MANUEL-Enzo/GameDuino/Organisation Projet/Cahier Des Charges Gameduino.docx

BENHARRATS Amine G4

MANUEL Enzo 2019/2020

CAHIER DES CHARGES :

Présentation :

Gameduino est une console de jeux vidéo portable de type Gameboy.

Notre projet est de concevoir notre propre Gameboy, ainsi que de coder nos propres jeux.

Les jeux seront orientés jeux d’arcades : les jeux que l’on pouvait auparavant jouer dans les bornes d’arcades (jeu dont le principe est relativement simple à comprendre et dont le but est généralement de faire le meilleur score possible).

Fiche technique :

La Gameduino sera composé de :

- Une carte arduino http://www.aliexpress.com/ (http://www.aliexpress.com/item/32850843888.html)
- Un interrupteur (pour allumer et éteindre la console) http://www.aliexpress.com/ (http://www.aliexpress.com/item/32921026422.html)
- Un écran https://fr.aliexpress.com/
- Un joystick (pour réaliser les déplacements dans les jeux) https://fr.aliexpress.com/ (https://fr.aliexpress.com/item/33007505063.html)
- Cinq boutons (pour réaliser les actions dans les jeux, modifier l’intensité du son et revenir au menu principale) https://fr.aliexpress.com/ (https://fr.aliexpress.com/%20)
- Un buzzer (permettant de faire des bruitages incorporés au jeu, ou des musiques) https://fr.aliexpress.com/

Contraintes :

Nous allons développer la partie programmation de notre projet dans le langage natif de l’Arduino, un langage proche du C et du C++. Comme notre Gameduino sera portable, il faudra que son aspect soit relativement soigné mais simple.

Résultats attendus :

Une console portable pratique à transporter avec divers jeux vidéo amusant pour passer le temps.
